andrempmattos/procsys-testsuite/instrumentation/som-exp-carrier/out/fig/pcb_top.png

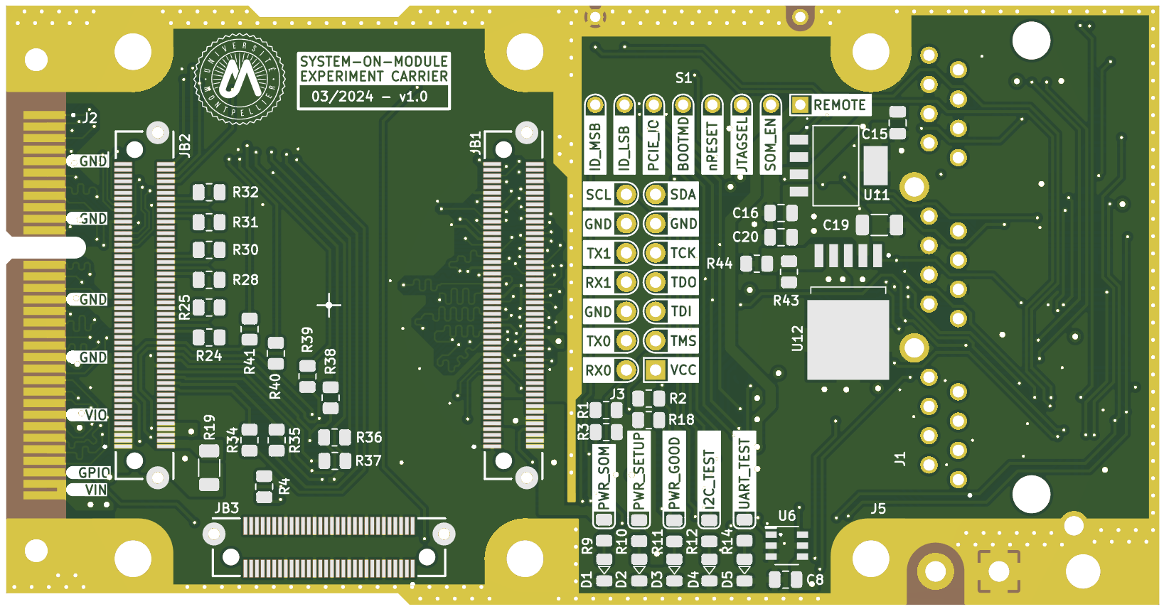
instrumentation/som-exp-carrier/out/fig/pcb_top.png
