andrempmattos/procsys-testsuite/instrumentation/som-exp-carrier/ref/som_connector_dimension.png

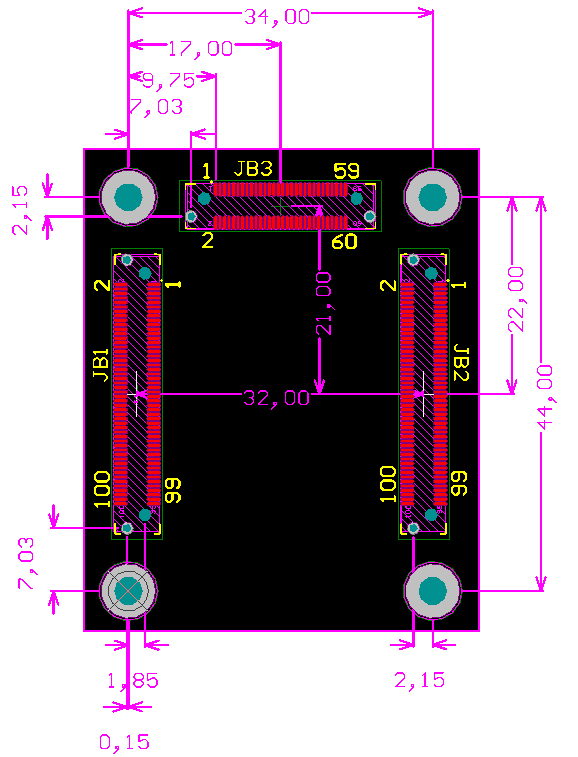
instrumentation/som-exp-carrier/ref/som_connector_dimension.png
