andrempmattos/procsys-testsuite/benchmarks/embench-freertos/hooks.c

/*
 * FreeRTOS V202212.00
 * Copyright (C) 2020 Amazon.com, Inc. or its affiliates.  All Rights Reserved.
 *
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
 * https://www.FreeRTOS.org
 * https://github.com/FreeRTOS
 *
 */

/******************************************************************************
 *
 * This file implements the code that is not demo specific, including the
 * hardware setup and standard FreeRTOS hook functions.
 *
 * ENSURE TO READ THE DOCUMENTATION PAGE FOR THIS PORT AND DEMO APPLICATION ON
 * THE http://www.FreeRTOS.org WEB SITE FOR FULL INFORMATION ON USING THIS DEMO
 * APPLICATION, AND ITS ASSOCIATE FreeRTOS ARCHITECTURE PORT!
 *
 */

#include "hooks.h"

/* FreeRTOS kernel includes. */
#include <FreeRTOS.h>
#include <task.h>

#include "inc/common.h"

/* Set to 1 to use direct mode and set to 0 to use vectored mode.

VECTOR MODE=Direct --> all traps into machine mode cause the pc to be set to the
vector base address (BASE) in the mtvec register.

VECTOR MODE=Vectored --> all synchronous exceptions into machine mode cause the
pc to be set to the BASE, whereas interrupts cause the pc to be set to the
address BASE plus four times the interrupt cause number.
*/
#define mainVECTOR_MODE_DIRECT	0

/*-----------------------------------------------------------*/

extern void freertos_risc_v_trap_handler( void );
extern void freertos_vector_table( void );

/*
 * Prototypes for the standard FreeRTOS callback/hook functions implemented
 * within this file.  See https://www.freertos.org/a00016.html
 */
void vApplicationMallocFailedHook( void );
void vApplicationIdleHook( void );
void vApplicationStackOverflowHook( TaskHandle_t pxTask, char *pcTaskName );
void vApplicationTickHook( void );

void prvSetupHardware( void )
{
    #if( mainVECTOR_MODE_DIRECT == 1 )
	{
		__asm__ volatile( "csrw mtvec, %0" :: "r"( freertos_risc_v_trap_handler ) );
	}
	#else
	{
		__asm__ volatile( "csrw mtvec, %0" :: "r"( ( uintptr_t )freertos_vector_table | 0x1 ) );
	}
	#endif
}
/*-----------------------------------------------------------*/

void vApplicationMallocFailedHook( void )
{
    /* vApplicationMallocFailedHook() will only be called if
     * configUSE_MALLOC_FAILED_HOOK is set to 1 in FreeRTOSConfig.h.  It is a hook
     * function that will get called if a call to pvPortMalloc() fails.
     * pvPortMalloc() is called internally by the kernel whenever a task, queue,
     * timer or semaphore is created.  It is also called by various parts of the
     * demo application.  If heap_1.c or heap_2.c are used, then the size of the
     * heap available to pvPortMalloc() is defined by configTOTAL_HEAP_SIZE in
     * FreeRTOSConfig.h, and the xPortGetFreeHeapSize() API function can be used
     * to query the size of free heap space that remains (although it does not
     * provide information on how the remaining heap might be fragmented). */
    taskDISABLE_INTERRUPTS();
    log_from_moncore_noheader_nospinlock("\n[FREERTOS] Malloc failed\n");
    for( ;; );
}
/*-----------------------------------------------------------*/

void vApplicationIdleHook( void )
{
    /* vApplicationIdleHook() will only be called if configUSE_IDLE_HOOK is set
     * to 1 in FreeRTOSConfig.h.  It will be called on each iteration of the idle
     * task.  It is essential that code added to this hook function never attempts
     * to block in any way (for example, call xQueueReceive() with a block time
     * specified, or call vTaskDelay()).  If the application makes use of the
     * vTaskDelete() API function (as this demo application does) then it is also
     * important that vApplicationIdleHook() is permitted to return to its calling
     * function, because it is the responsibility of the idle task to clean up
     * memory allocated by the kernel to any task that has since been deleted. */
}
/*-----------------------------------------------------------*/

void vApplicationStackOverflowHook( TaskHandle_t pxTask, char *pcTaskName )
{
    ( void ) pcTaskName;
    ( void ) pxTask;

    /* Run time stack overflow checking is performed if
     * configCHECK_FOR_STACK_OVERFLOW is defined to 1 or 2.  This hook
     * function is called if a stack overflow is detected. */
    taskDISABLE_INTERRUPTS();
    log_from_moncore_noheader_nospinlock("\n[FREERTOS] Stack overflow\n");
    for( ;; );
}
/*-----------------------------------------------------------*/

void vApplicationTickHook( void )
{
    /* Nothing to be done */
}
/*-----------------------------------------------------------*/

void vAssertCalled( void )
{
    volatile uint32_t ul;
    const uint32_t ulNullLoopDelay = 0x1ffffUL;

    taskDISABLE_INTERRUPTS();

    /* Send a msg to indicate that assert was hit - interrupts are off
     * here to prevent any further tick interrupts or context switches, so the
     * delay is implemented as a crude loop instead of a peripheral timer. */
    
    log_from_moncore_noheader_nospinlock("\n[FREERTOS] Assert triggered\n");
    for( ;; )
    {
        for( ul = 0; ul < ulNullLoopDelay; ul++ )
        {
            __asm volatile( "nop" );
        }
    }
}
/*-----------------------------------------------------------*/
