andrempmattos/procsys-testsuite/instrumentation/host-fpga-src/script/convert_tmp100_values.py

"""
  Convert TMP100 received Hex values to temperature in °C

  This script will take the received hex values from the temperature register of the sensor 
  and convert it to decimal values.
"""

"""
 1. TODO Add steps to convert

 Examples values:
 TODO Add example values
 """
